Ikeen/heidi/frontend/img/background.jpeg

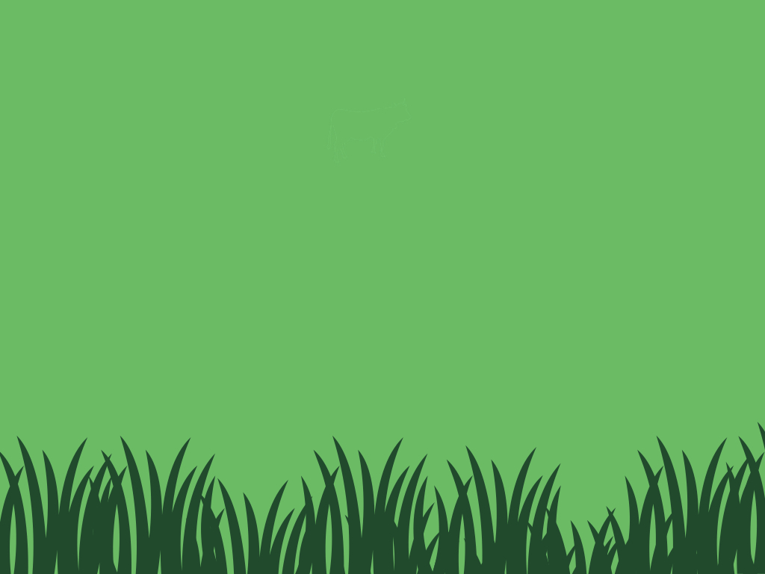
frontend/img/background.jpeg
