Ikeen/heidi/frontend/img/kuh_green.png

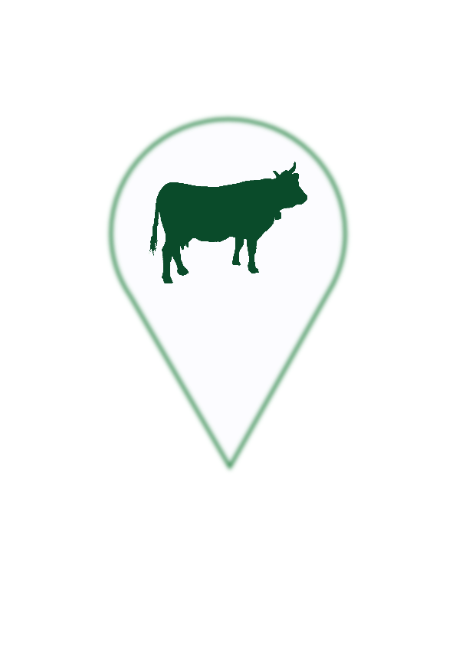
frontend/img/kuh_green.png
