Ikeen/heidi/cad/GatewayTracker/PrintFrameBox.FCStd

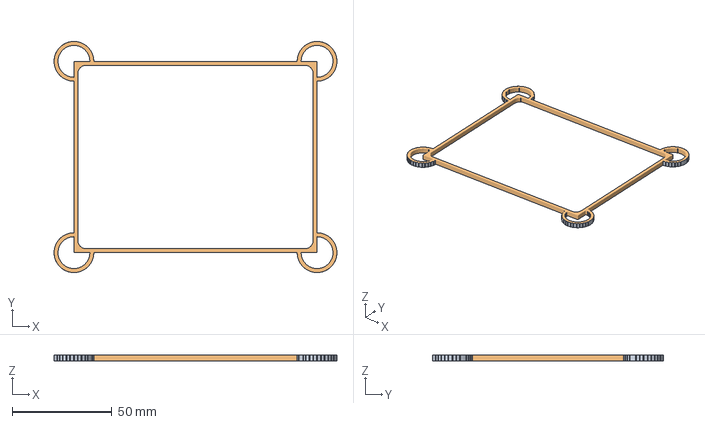
[picture p26: CAD file, 2022-04-28]
cad/GatewayTracker/PrintFrameBox.FCStd
142.0 x 116.0 x 3.00 mm
Fillet (Meshed)
