Ikeen/heidi/cad/Clips/GPSBoardClip.fcstd

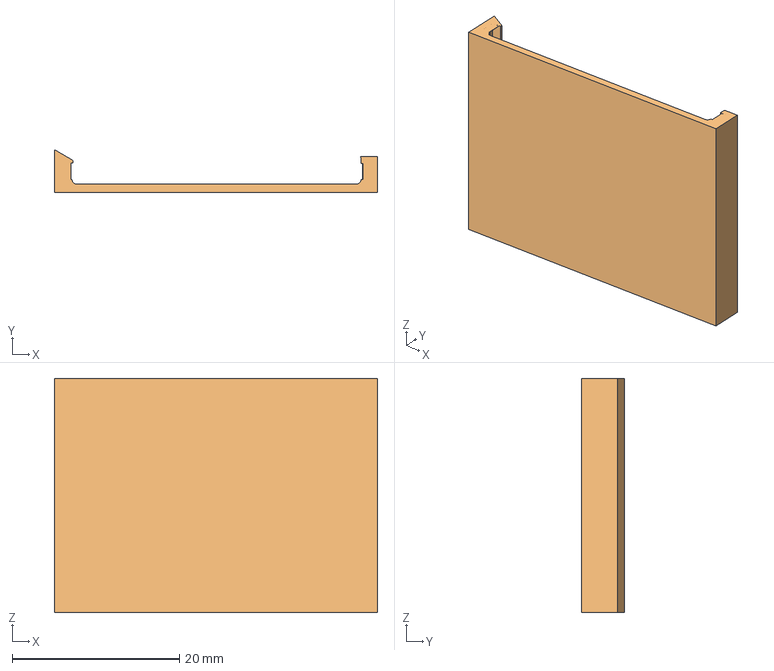
[picture p27: CAD file, 2022-03-31]
cad/Clips/GPSBoardClip.fcstd
38.6 x 5.08 x 28.0 mm
Fillet002 (Meshed)
