Ikeen/heidi/cad/GatewayTracker/BoxBottomGateway.fcstd

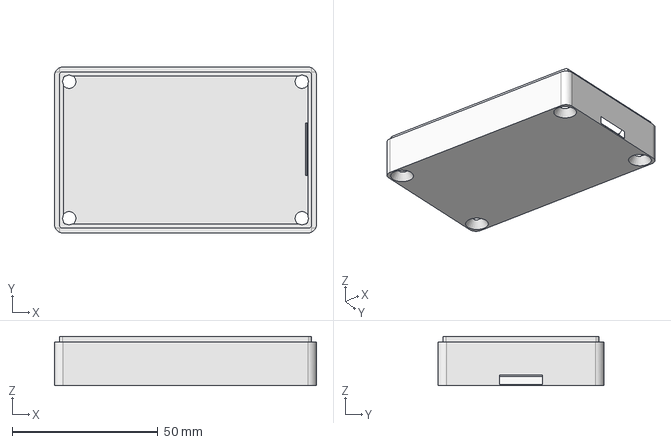
[picture p28: CAD file, 2022-04-28]
cad/GatewayTracker/BoxBottomGateway.fcstd
90.0 x 57.0 x 17.0 mm
