Ikeen/heidi/cad/Clips/GSMBoardClip.fcstd

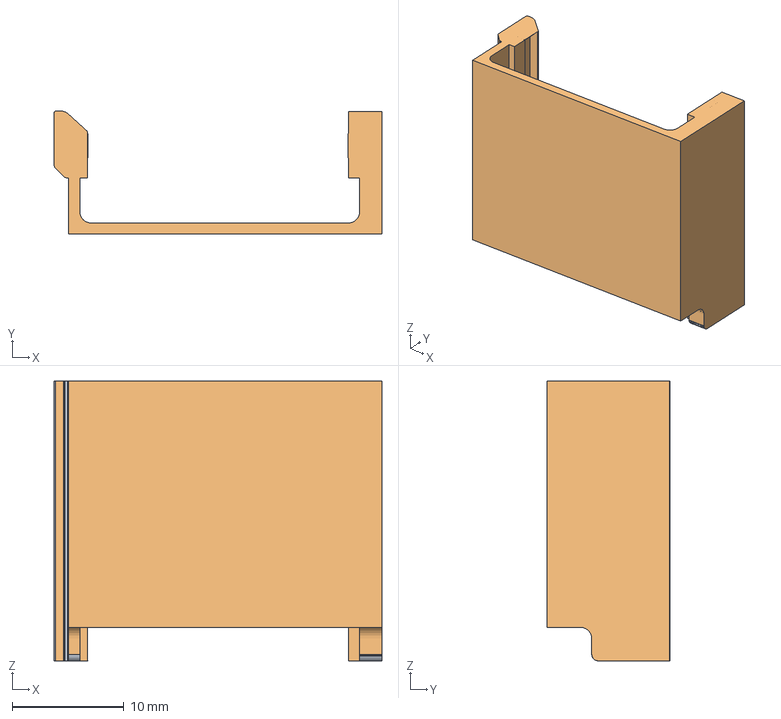
[picture p29: CAD file, 2022-03-31]
cad/Clips/GSMBoardClip.fcstd
29.3 x 11.0 x 25.0 mm
Fillet003 (Meshed)
