Ikeen/heidi/cad/GatewayTracker/MidBoxTop.fcstd

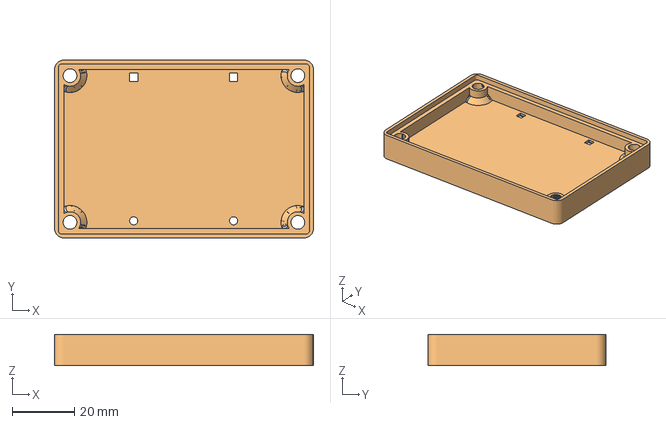
[picture p30: CAD file, 2022-03-31]
cad/GatewayTracker/MidBoxTop.fcstd
83.0 x 57.0 x 10.0 mm
Chamfer001 (Meshed)
