Ikeen/heidi/cad/Clips/CableClip.fcstd

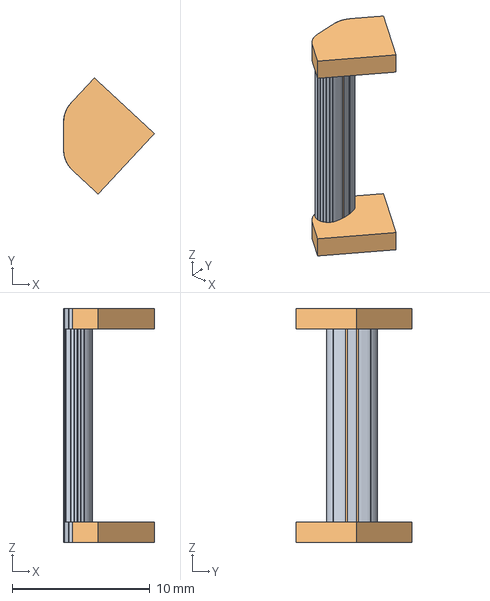
[picture p31: CAD file, 2022-03-31]
cad/Clips/CableClip.fcstd
6.60 x 8.45 x 17.0 mm
Fusion (Meshed)
