Ikeen/heidi/cad/GatewayTracker/BoxTopGateway.fcstd

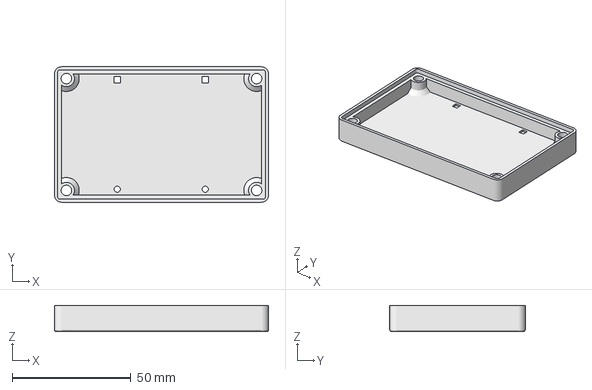
[picture p32: CAD file, 2022-03-31]
cad/GatewayTracker/BoxTopGateway.fcstd
90.0 x 57.0 x 11.0 mm
