Ikeen/heidi/cad/Clips/GPSAntennaClip3.fcstd

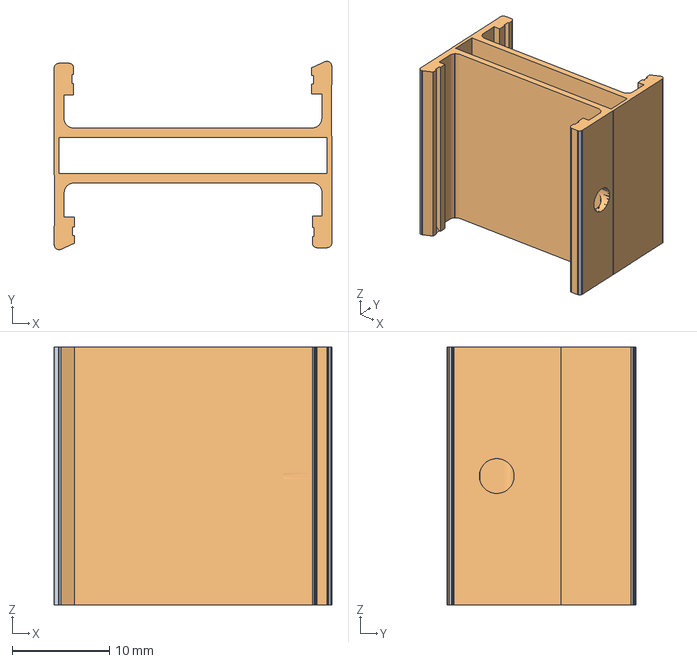
[picture p33: CAD file, 2022-03-31]
cad/Clips/GPSAntennaClip3.fcstd
28.6 x 19.4 x 26.5 mm
Fusion002 (Meshed)
