Ikeen/heidi/cad/Clips/GPSAntennaClip.fcstd

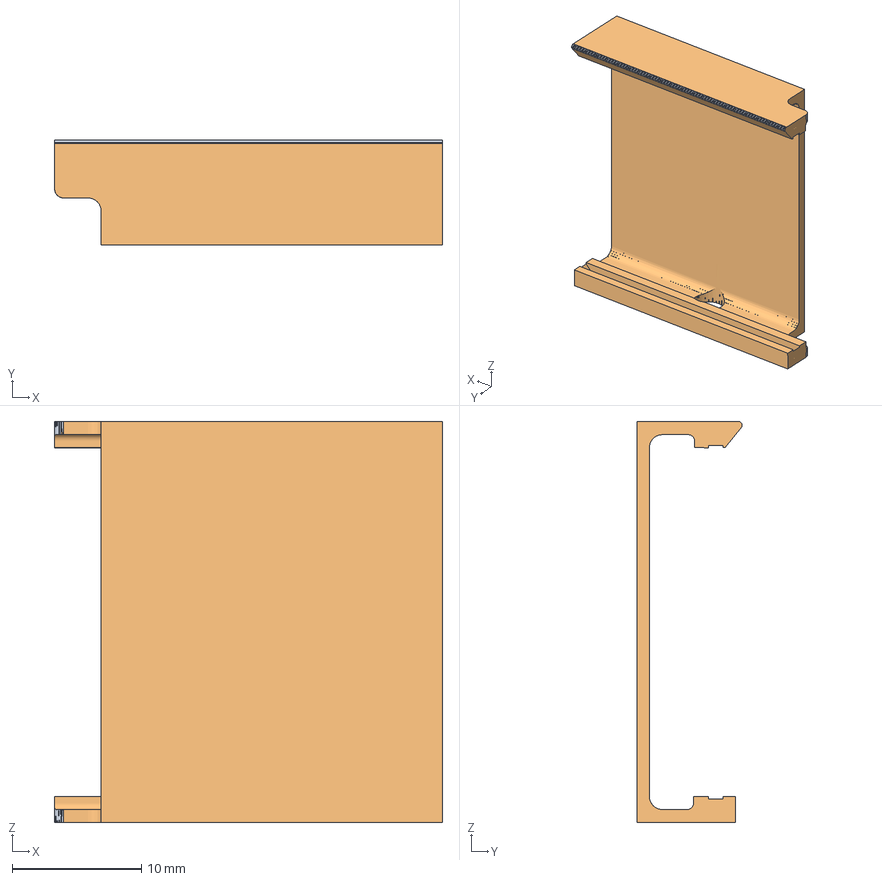
[picture p34: CAD file, 2021-10-14]
cad/Clips/GPSAntennaClip.fcstd
30.0 x 8.13 x 31.0 mm
Fillet006 (Meshed)
