Ikeen/heidi/cad/Clips/12mmClip.FCStd

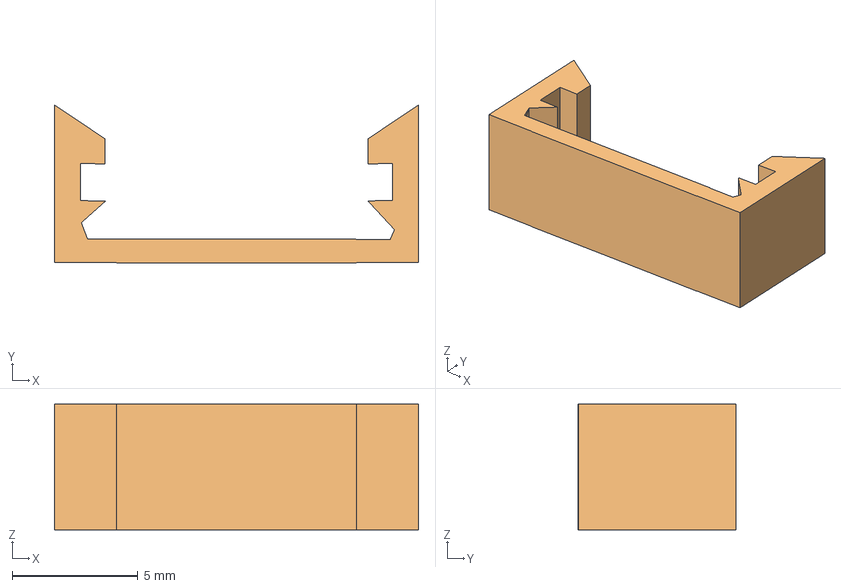
[picture p35: CAD file, 2021-05-17]
cad/Clips/12mmClip.FCStd
14.5 x 6.30 x 5.00 mm
Fusion (Meshed)
