Ikeen/heidi/cad/Clips/12mmBoardClip.stl

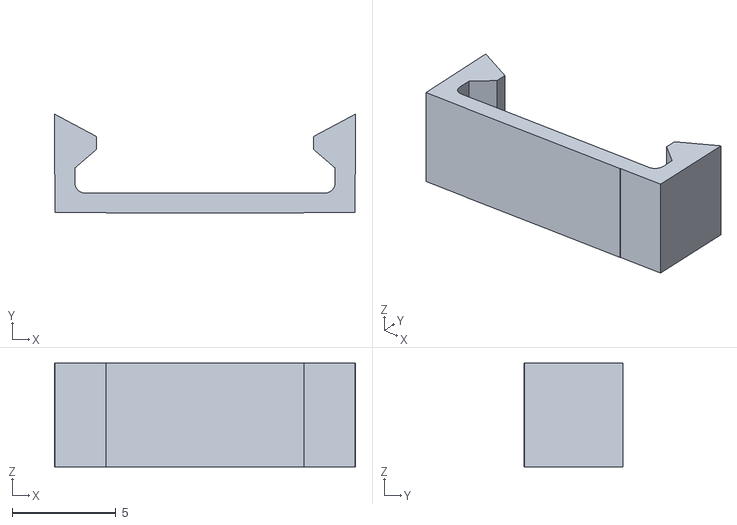
[picture p36: CAD file, 2021-05-17]
cad/Clips/12mmBoardClip.stl
14.5 x 4.78 x 5.00
