Ikeen/heidi/cad/Clips/21mmClip.FCStd

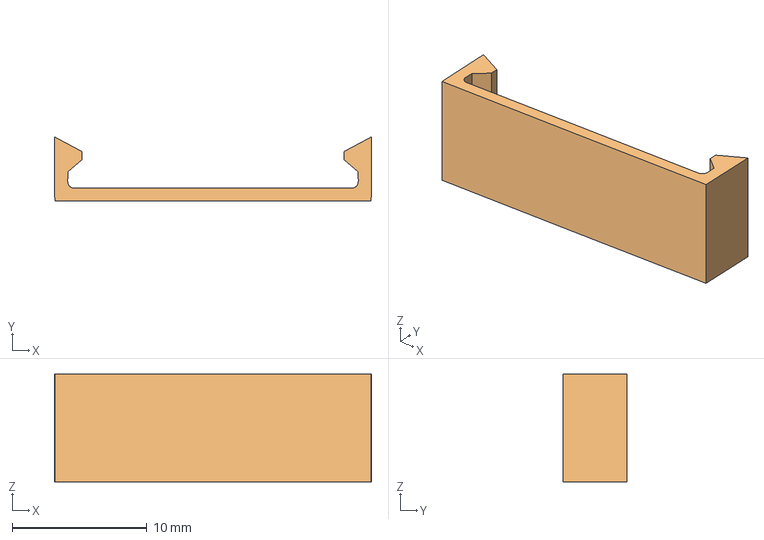
[picture p37: CAD file, 2021-05-17]
cad/Clips/21mmClip.FCStd
23.5 x 4.78 x 8.00 mm
Fusion (Meshed)
