Ikeen/heidi/cad/Clips/21mmBoardClip.stl

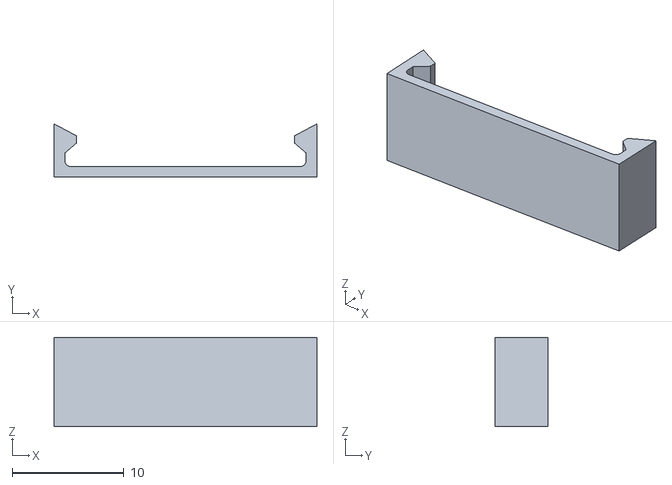
[picture p38: CAD file, 2021-05-17]
cad/Clips/21mmBoardClip.stl
23.5 x 4.78 x 8.00
