Ikeen/heidi/cad/Clips/AccelClip.stl

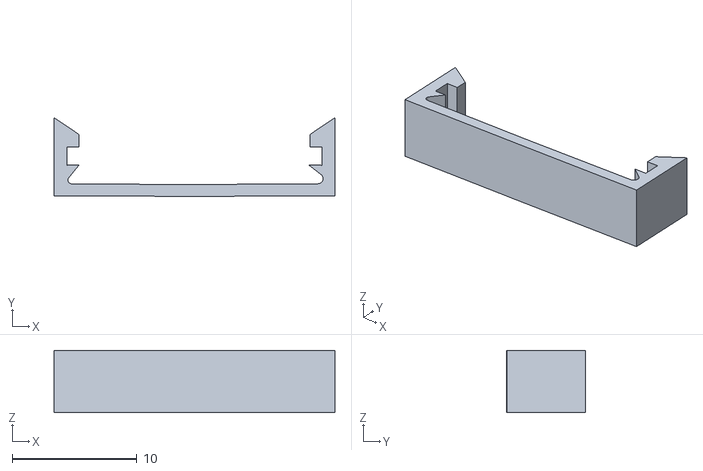
[picture p39: CAD file, 2021-05-17]
cad/Clips/AccelClip.stl
22.5 x 6.30 x 5.00
