Ikeen/heidi/cad/Clips/ArduinoClip.fcstd

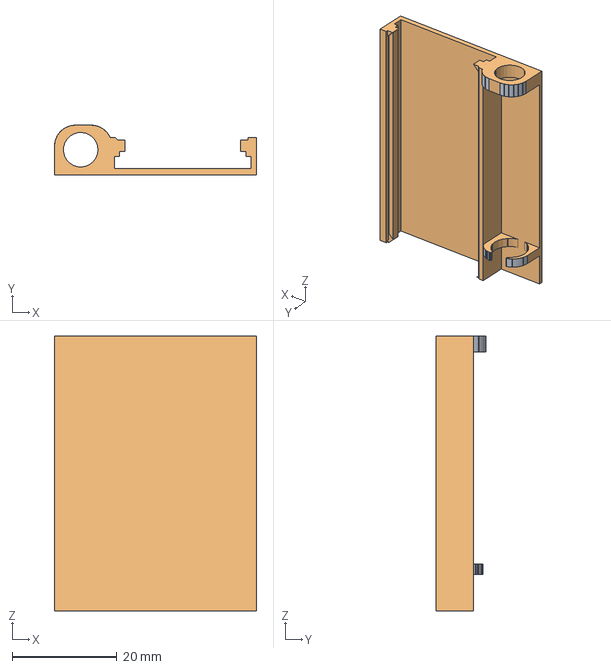
[picture p40: CAD file, 2020-06-02]
cad/Clips/ArduinoClip.fcstd
38.6 x 9.50 x 52.5 mm
Fusion (Meshed)
