Ikeen/heidi/backend/heidi-secrets.h

/*
 * heidi-secrets.h
 *
 *  Created on: 14.10.2021
 *      Author: frank
 */

#ifndef HEIDI_SECRETS_H_
#define HEIDI_SECRETS_H_

//#define HEIDI_SERVER_PUSH_URL put your URL here like: "https://1234567890.myfritz.net:123/push_data64.php"
#ifndef HEIDI_SERVER_PUSH_URL
#error "no push URL set"
#endif

//#define SIM_PIN put your PIN here like: "0000"
#ifndef HEIDI_SERVER_PUSH_URL
#error "no PIN set"
#endif

#endif /* HEIDI_SECRETS_H_ */
